PedPEx/JWST-Keychain/pictures/v1_3.jpg

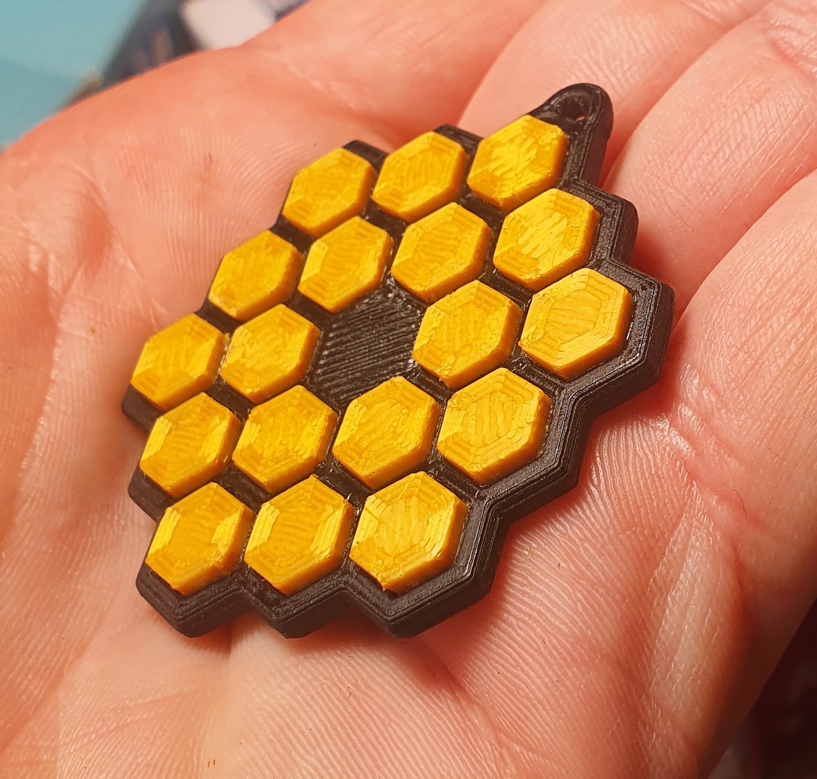
pictures/v1_3.jpg
