PedPEx/JWST-Keychain/pictures/v1_Base_2.jpg

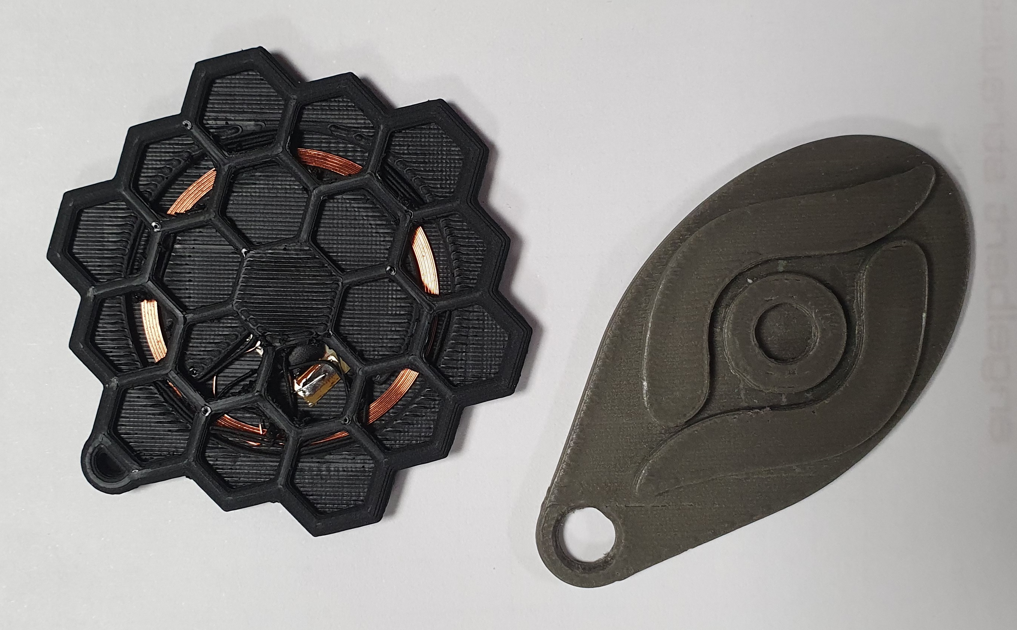
pictures/v1_Base_2.jpg
