PedPEx/JWST-Keychain/pictures/v3_3.jpg

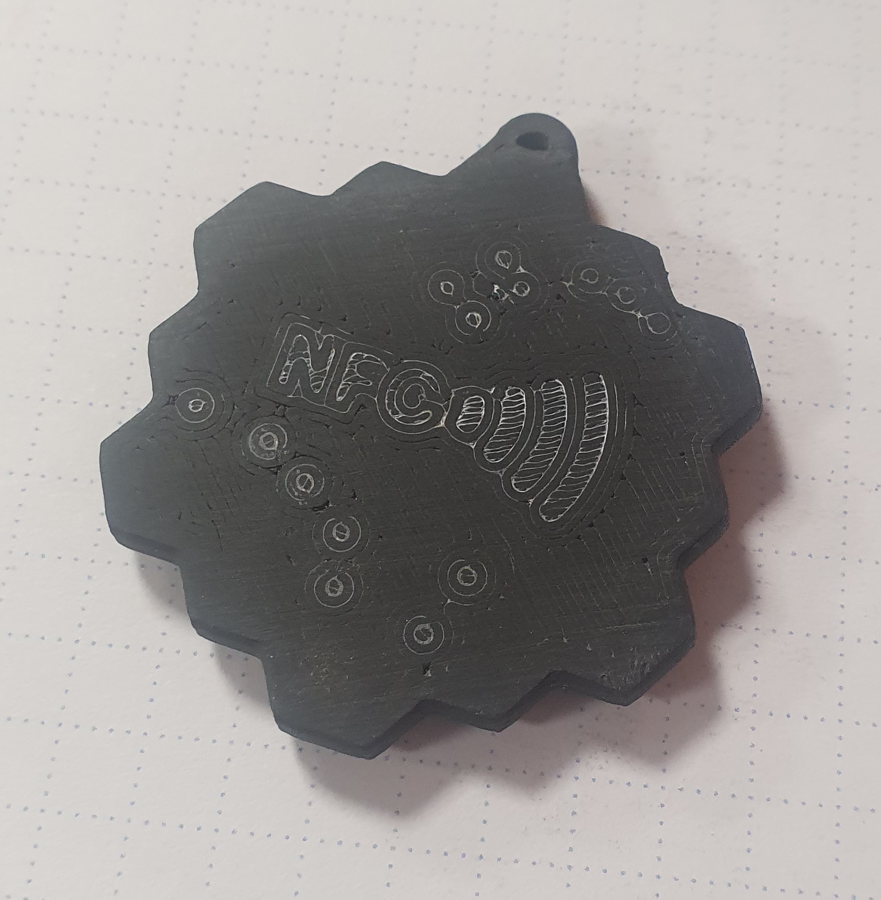
pictures/v3_3.jpg
