PedPEx/JWST-Keychain/pictures/v3_6.jpg

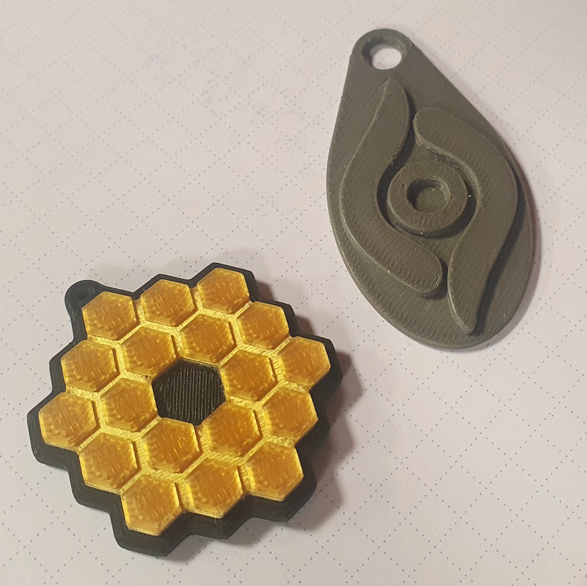
pictures/v3_6.jpg
