PedPEx/JWST-Keychain/pictures/v3_7.jpg

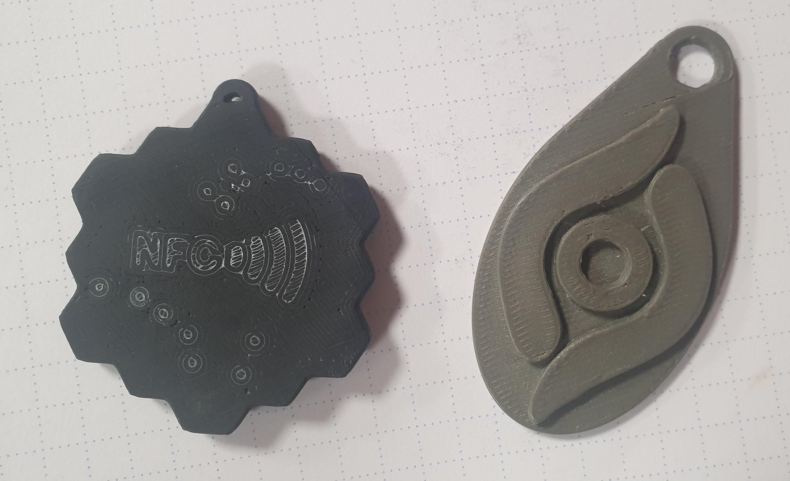
pictures/v3_7.jpg
