PedPEx/JWST-Keychain/pictures/z_Constellation_Readable_TestPrint_1.jpg

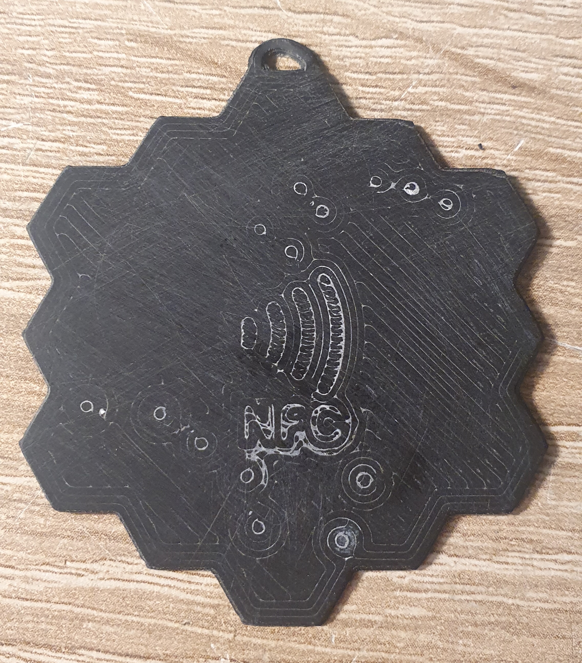
pictures/z_Constellation_Readable_TestPrint_1.jpg
