PedPEx/JWST-Keychain/pictures/z_Constellation_Readable_TestPrint_2.jpg

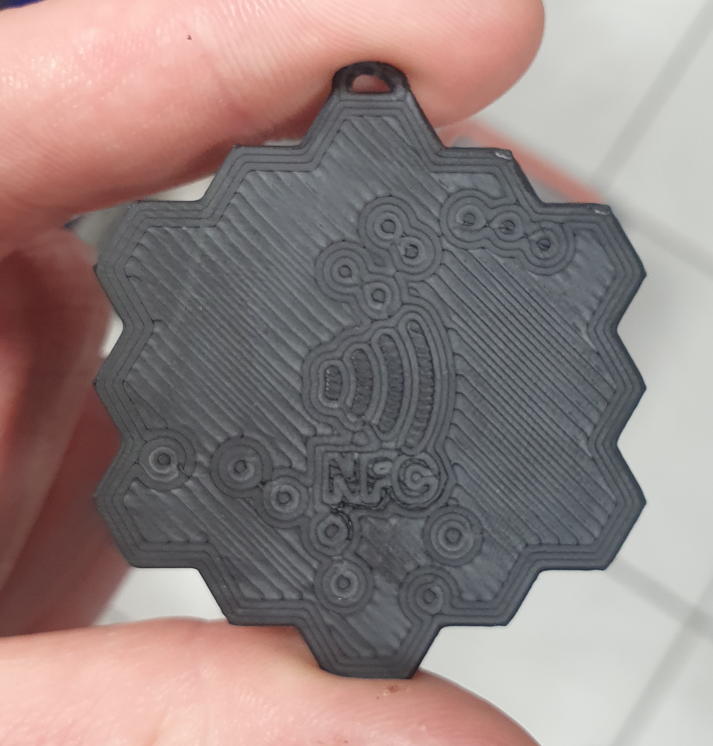
pictures/z_Constellation_Readable_TestPrint_2.jpg
